TheCurby/wordclock-stm32wb55/images/IMG3.JPG

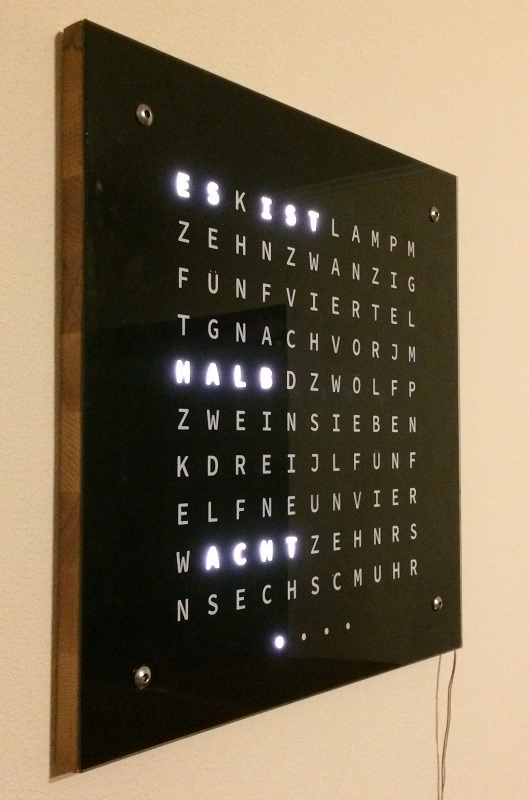
images/IMG3.JPG
